TheCyberWeaver/NixieTube001/ui_controlPanel.py

# -*- coding: utf-8 -*-

################################################################################
## Form generated from reading UI file 'controlPanel.ui'
##
## Created by: Qt User Interface Compiler version 6.4.2
##
## WARNING! All changes made in this file will be lost when recompiling UI file!
################################################################################

from PySide6.QtCore import (QCoreApplication, QDate, QDateTime, QLocale,
    QMetaObject, QObject, QPoint, QRect,
    QSize, QTime, QUrl, Qt)
from PySide6.QtGui import (QBrush, QColor, QConicalGradient, QCursor,
    QFont, QFontDatabase, QGradient, QIcon,
    QImage, QKeySequence, QLinearGradient, QPainter,
    QPalette, QPixmap, QRadialGradient, QTransform)
from PySide6.QtWidgets import (QApplication, QHBoxLayout, QLabel, QPushButton,
    QSizePolicy, QVBoxLayout, QWidget)

class Ui_Form(object):
    def setupUi(self, Form):
        if not Form.objectName():
            Form.setObjectName(u"Form")
        Form.resize(481, 276)
        self.verticalLayout = QVBoxLayout(Form)
        self.verticalLayout.setObjectName(u"verticalLayout")
        self.label = QLabel(Form)
        self.label.setObjectName(u"label")
        self.label.setMaximumSize(QSize(16777215, 50))
        self.label.setStyleSheet(u"font: 20pt \"Segoe UI\";")
        self.label.setAlignment(Qt.AlignCenter)

        self.verticalLayout.addWidget(self.label)

        self.pushButton = QPushButton(Form)
        self.pushButton.setObjectName(u"pushButton")

        self.verticalLayout.addWidget(self.pushButton)

        self.pushButton_2 = QPushButton(Form)
        self.pushButton_2.setObjectName(u"pushButton_2")

        self.verticalLayout.addWidget(self.pushButton_2)

        self.horizontalLayout = QHBoxLayout()
        self.horizontalLayout.setObjectName(u"horizontalLayout")

        self.verticalLayout.addLayout(self.horizontalLayout)

        self.label_2 = QLabel(Form)
        self.label_2.setObjectName(u"label_2")

        self.verticalLayout.addWidget(self.label_2)


        self.retranslateUi(Form)

        QMetaObject.connectSlotsByName(Form)
    # setupUi

    def retranslateUi(self, Form):
        Form.setWindowTitle(QCoreApplication.translate("Form", u"Form", None))
        self.label.setText(QCoreApplication.translate("Form", u"Nixie Tube", None))
        self.pushButton.setText(QCoreApplication.translate("Form", u"PushButton", None))
        self.pushButton_2.setText(QCoreApplication.translate("Form", u"PushButton", None))
        self.label_2.setText(QCoreApplication.translate("Form", u"TextLabel", None))
    # retranslateUi
